cbonsig/openclock/enclosure_design/2D_rev2/uno-assy/RAPC732.sldprt

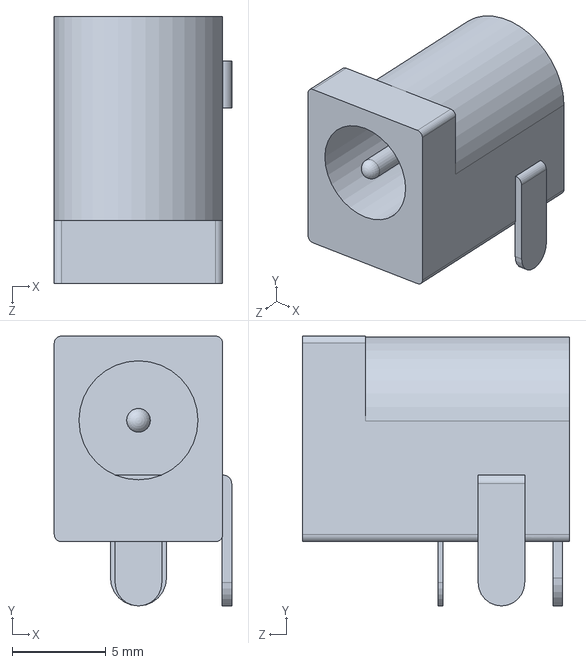
[picture p21: CAD file, 2013-04-10]
enclosure_design/2D_rev2/uno-assy/RAPC732.sldprt
9.47 x 14.4 x 14.2 mm
