cbonsig/openclock/enclosure_design/2D_rev2/wave_shield.SLDPRT

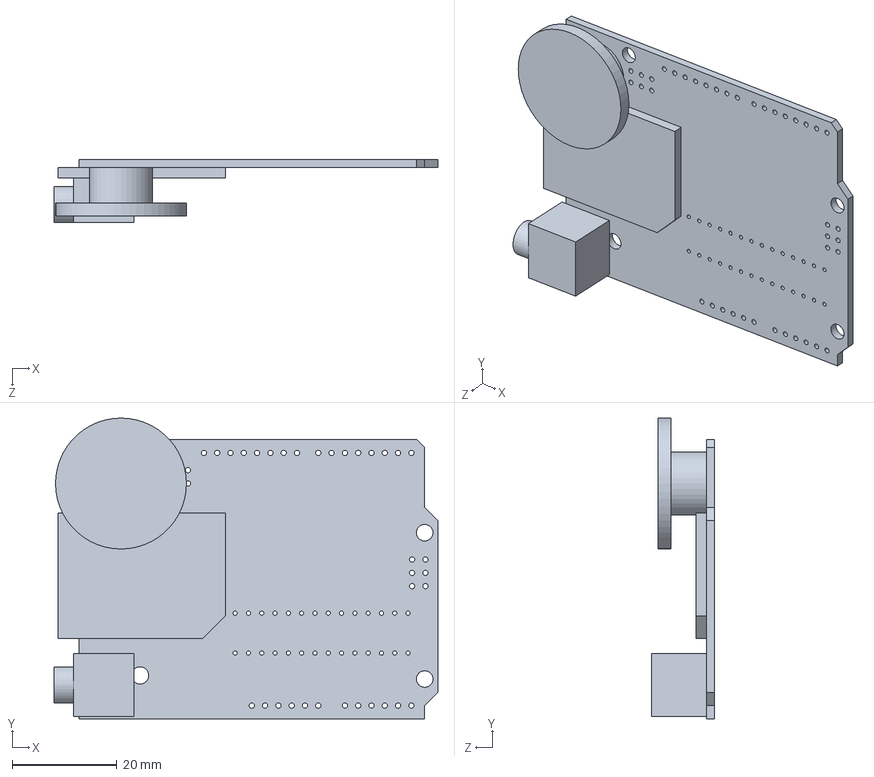
[picture p22: CAD file, 2013-05-05]
enclosure_design/2D_rev2/wave_shield.SLDPRT
73.3 x 57.4 x 12.1 mm
