cbonsig/openclock/enclosure_design/3D_rev1/base_side.SLDPRT

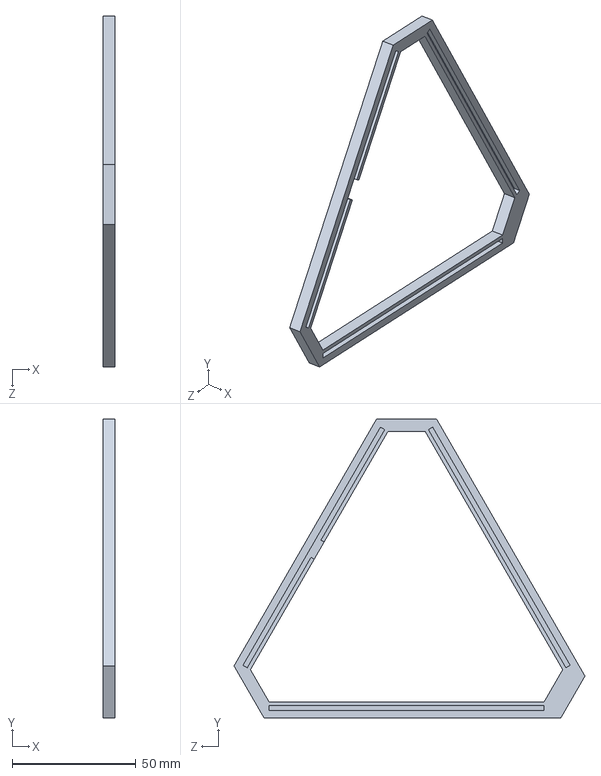
[picture p23: CAD file, 2012-08-22]
enclosure_design/3D_rev1/base_side.SLDPRT
5.00 x 120.6 x 141.6 mm
