cbonsig/openclock/enclosure_design/2D_rev2/uno-assy/SW3dPS-67068-0000-molex.SLDPRT

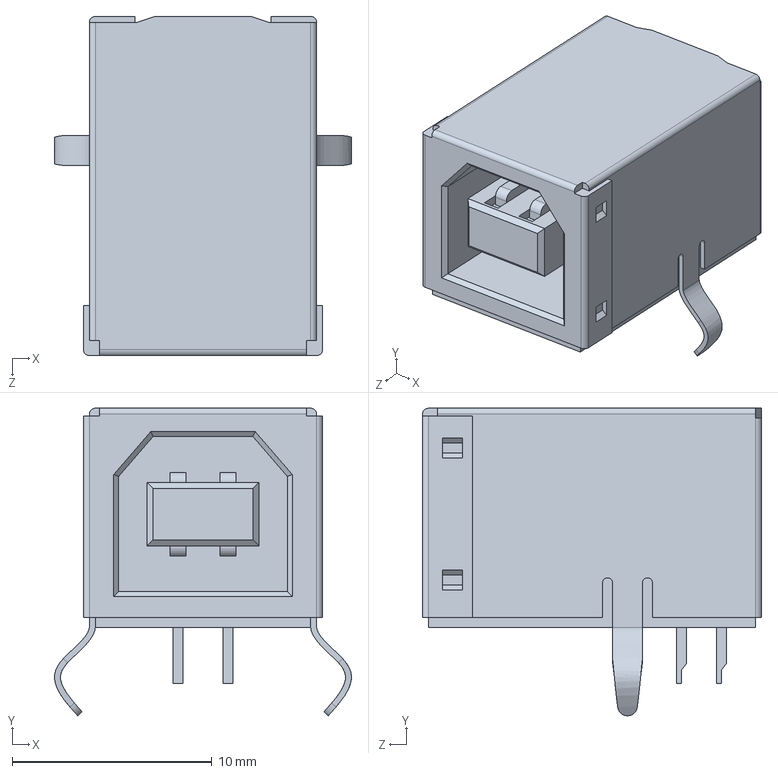
[picture p24: CAD file, 2013-04-10]
enclosure_design/2D_rev2/uno-assy/SW3dPS-67068-0000-molex.SLDPRT
14.9 x 15.4 x 17.0 mm
