cbonsig/openclock/enclosure_design/3D_rev1/SureElectronics_32x16_DE-DP14112.SLDPRT

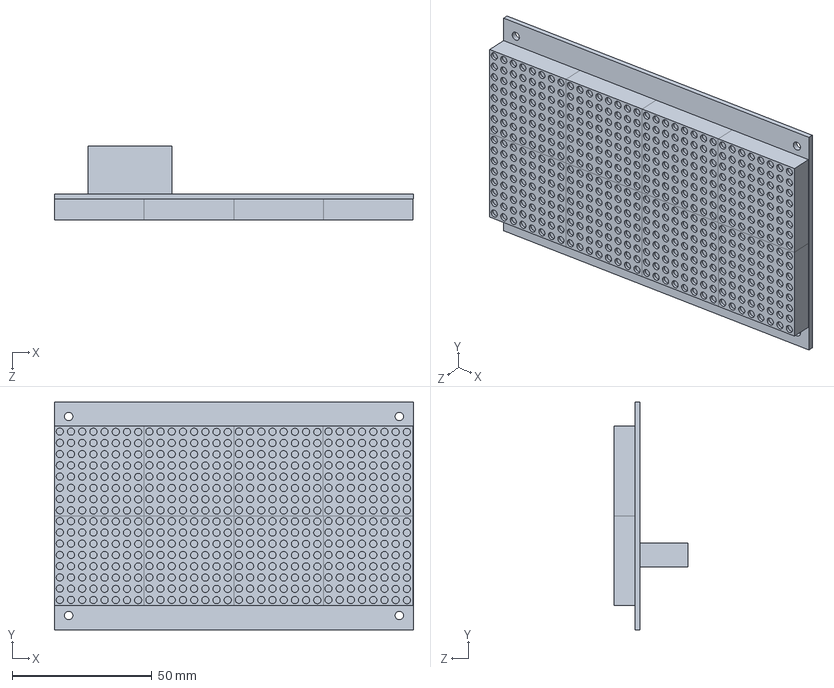
[picture p25: CAD file, 2012-08-22]
enclosure_design/3D_rev1/SureElectronics_32x16_DE-DP14112.SLDPRT
128.3 x 81.3 x 26.3 mm
