cbonsig/openclock/enclosure_design/2D_rev2/uno-assy/C-0534237-04-3.SLDPRT

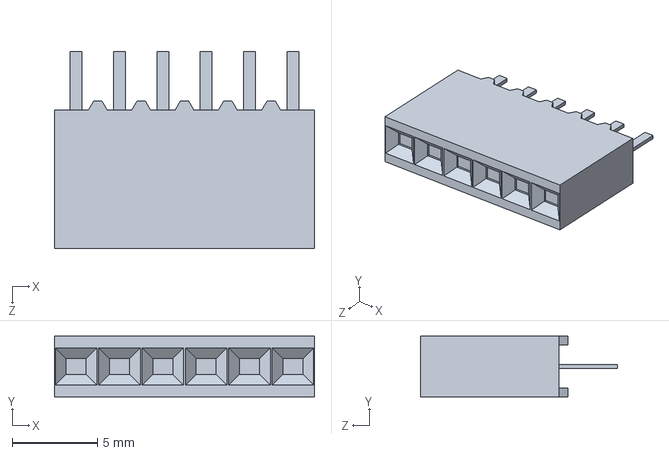
[picture p26: CAD file, 2013-04-10]
enclosure_design/2D_rev2/uno-assy/C-0534237-04-3.SLDPRT
15.2 x 3.56 x 11.6 mm
