cbonsig/openclock/enclosure_design/3D_rev1/3in_speaker.SLDPRT

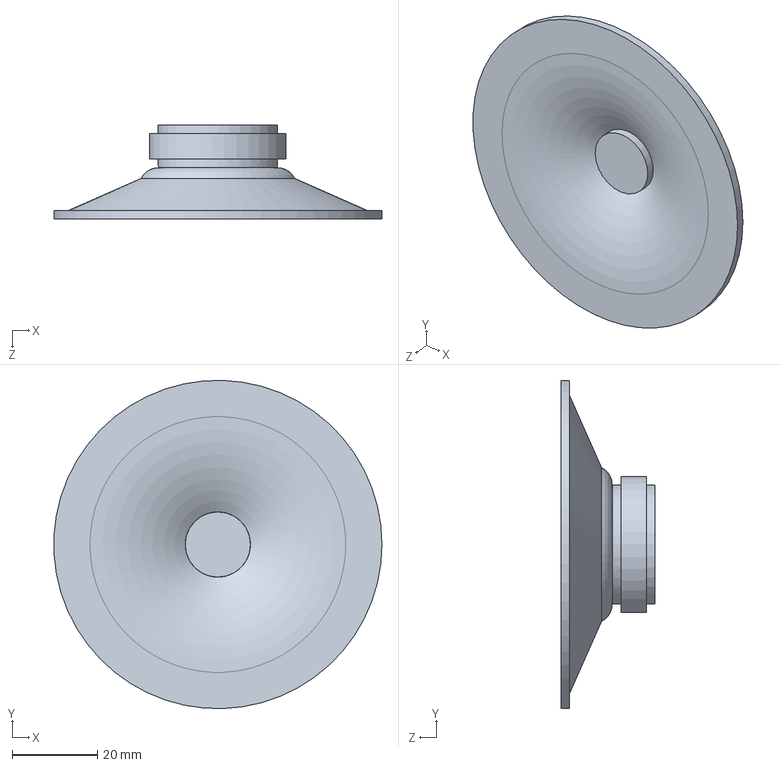
[picture p27: CAD file, 2012-08-22]
enclosure_design/3D_rev1/3in_speaker.SLDPRT
76.9 x 77.0 x 22.0 mm
