cbonsig/openclock/enclosure_design/2D_rev2/2D_Enclosure_Rev2_Curved.SLDPRT

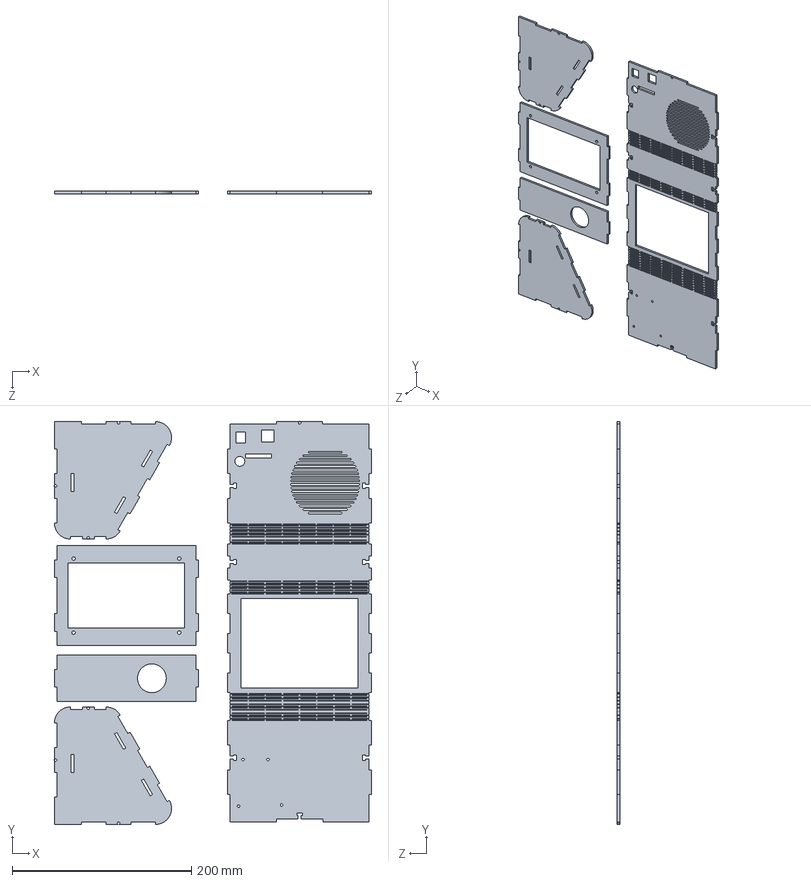
[picture p28: CAD file, 2013-05-04]
enclosure_design/2D_rev2/2D_Enclosure_Rev2_Curved.SLDPRT
354.4 x 449.9 x 3.00 mm
