cbonsig/openclock/enclosure_design/3D_rev1/Fujitsu_4wire_6.4in_N010-0554-T048.SLDPRT

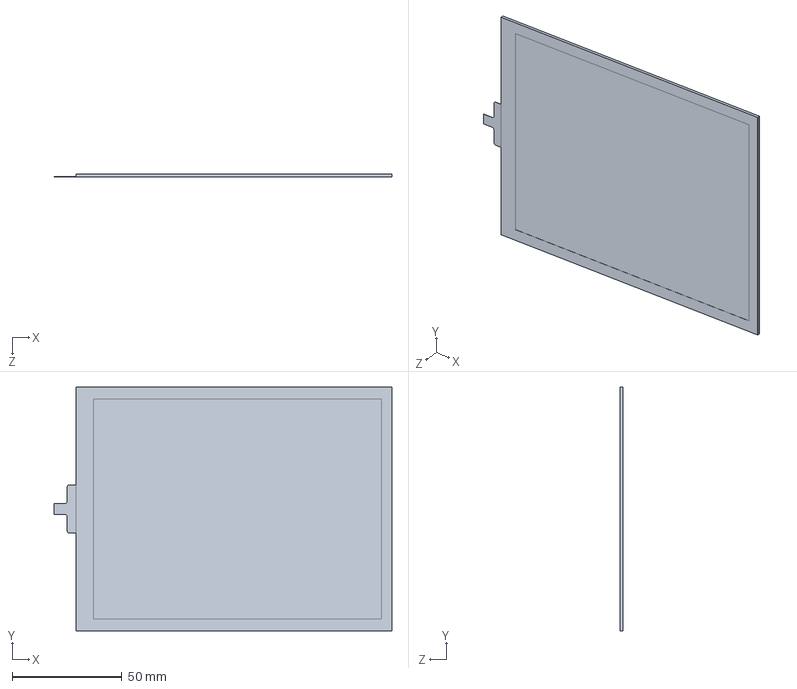
[picture p29: CAD file, 2012-08-22]
enclosure_design/3D_rev1/Fujitsu_4wire_6.4in_N010-0554-T048.SLDPRT
154.0 x 111.0 x 1.40 mm
