cbonsig/openclock/schematics/protoshield_bottom_wiring.png

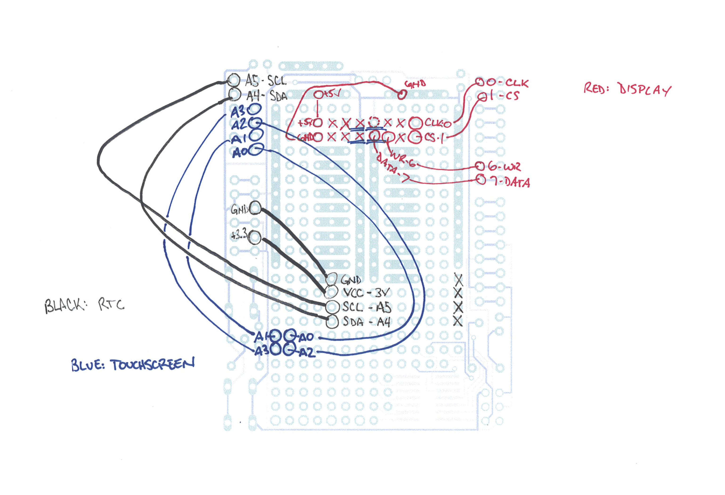
schematics/protoshield_bottom_wiring.png
